opsecpanda/Panda41/Panda41-pics/buddies at monument.jpg

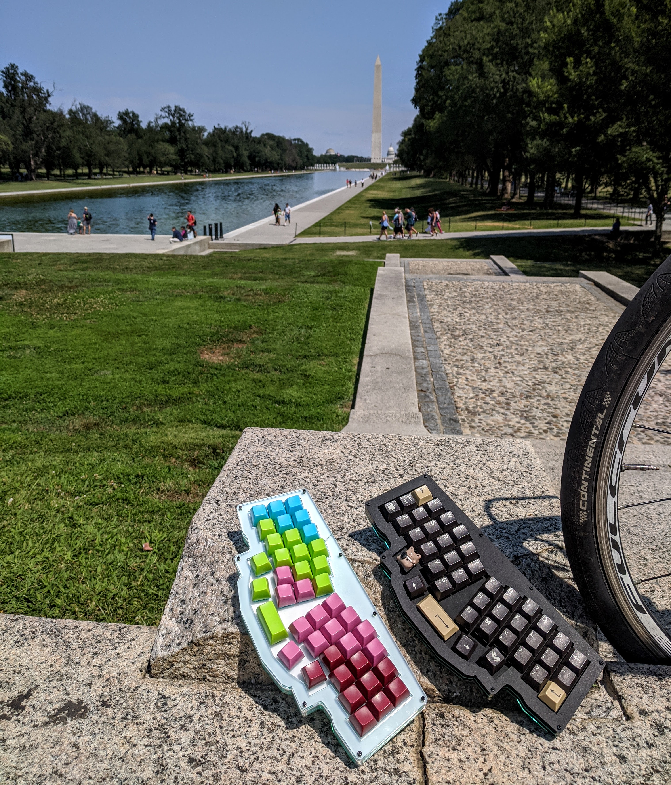
Panda41-pics/buddies at monument.jpg
