opsecpanda/Panda41/Panda41-pics/cafe and shale.jpg

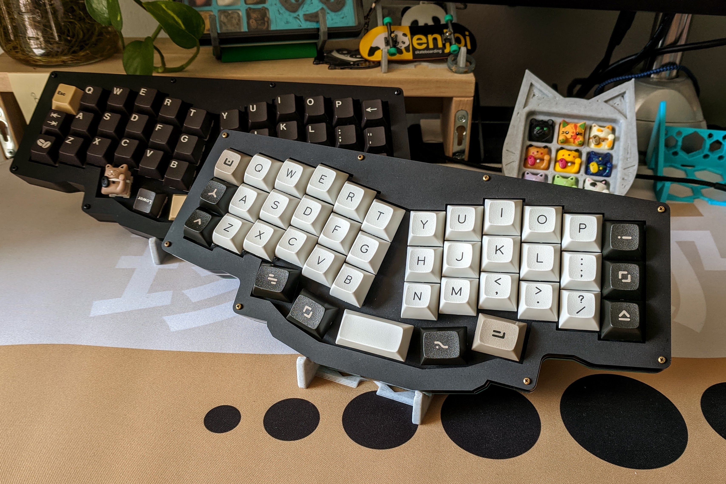
Panda41-pics/cafe and shale.jpg
