opsecpanda/Panda41/Panda41-pics/DSS Drank and RGB layer.jpg

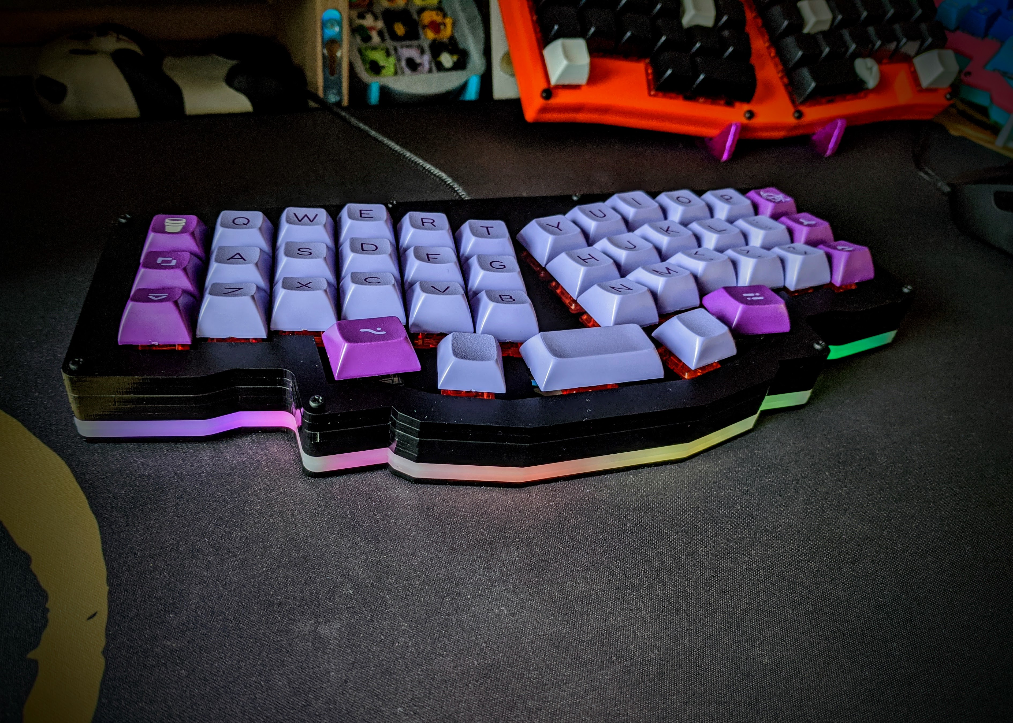
Panda41-pics/DSS Drank and RGB layer.jpg
